SCLW/CMOS_Synthesizer/assets/exports/10-prng-cd4094-cd4070.pdf

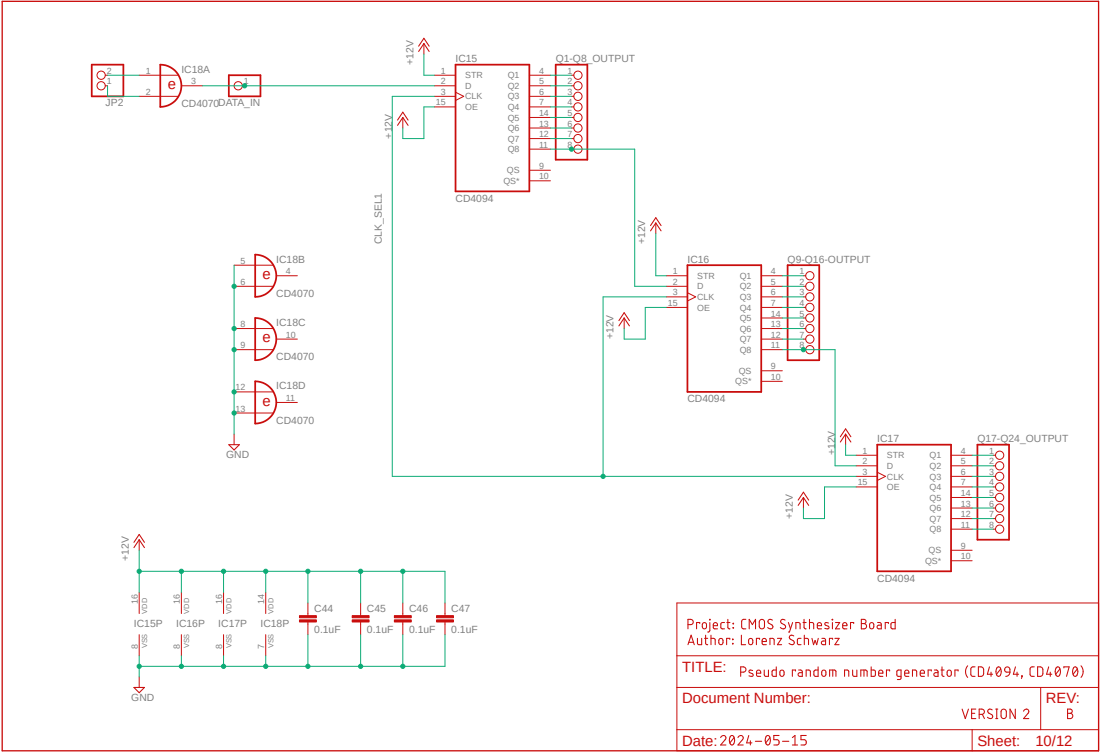
[picture p25: page 1]
