SCLW/CMOS_Synthesizer/assets/exports/11-mixing-section-lm358.pdf

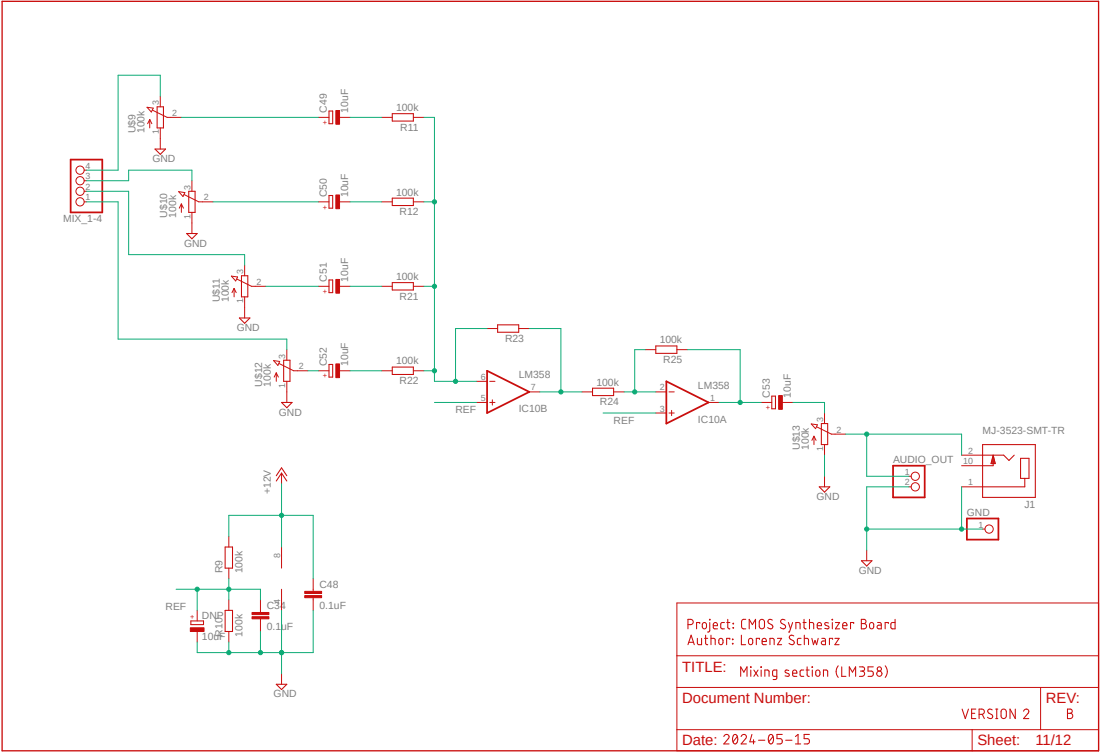
[picture p26: page 1]
