SCLW/CMOS_Synthesizer/assets/exports/12-rotary-switches.pdf

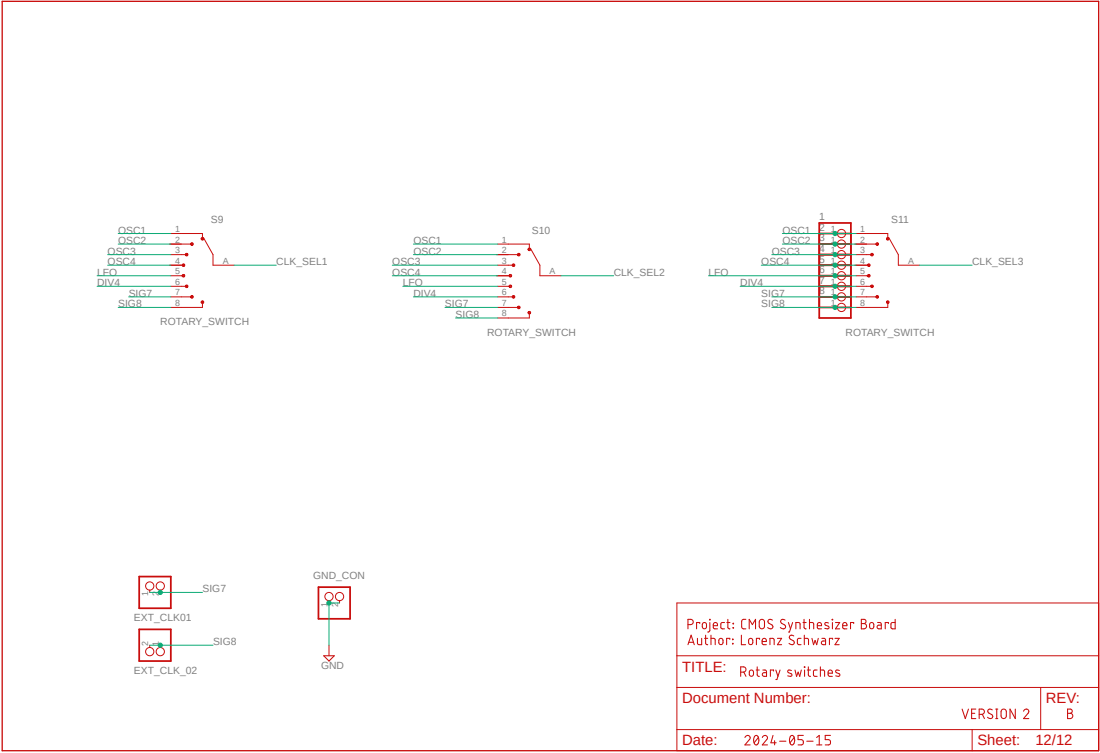
[picture p27: page 1]

Document Number: | REV:
