SCLW/CMOS_Synthesizer/assets/exports/deadlock-prevention-circuit-cd4068-cd4070-cd4077.pdf

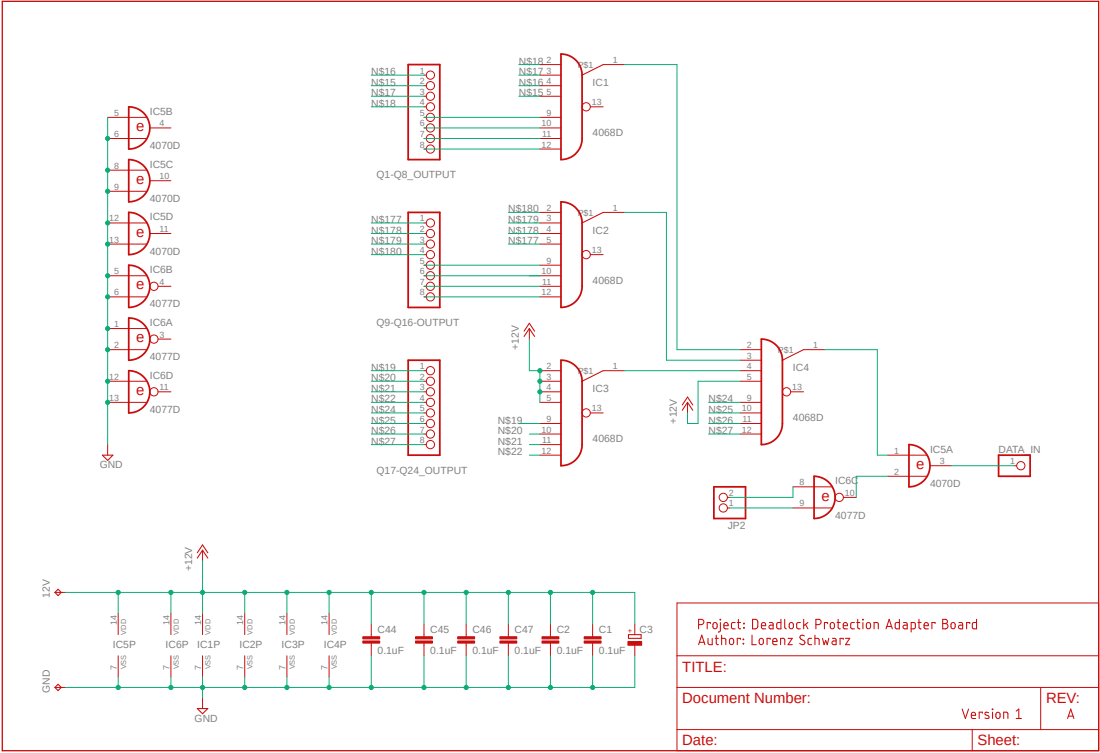
[picture p28: page 1]
