SCLW/CMOS_Synthesizer/assets/exports/dimensions.pdf

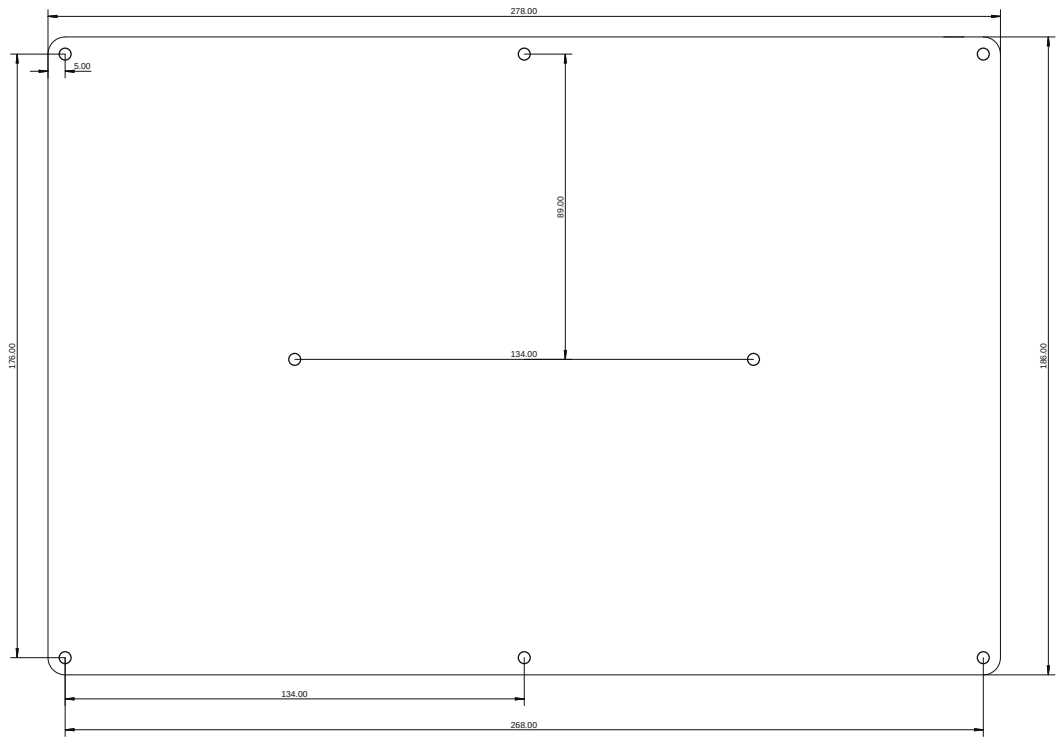
[picture p29: page 1]
