SCLW/CMOS_Synthesizer/assets/exports/main-board-traces.pdf

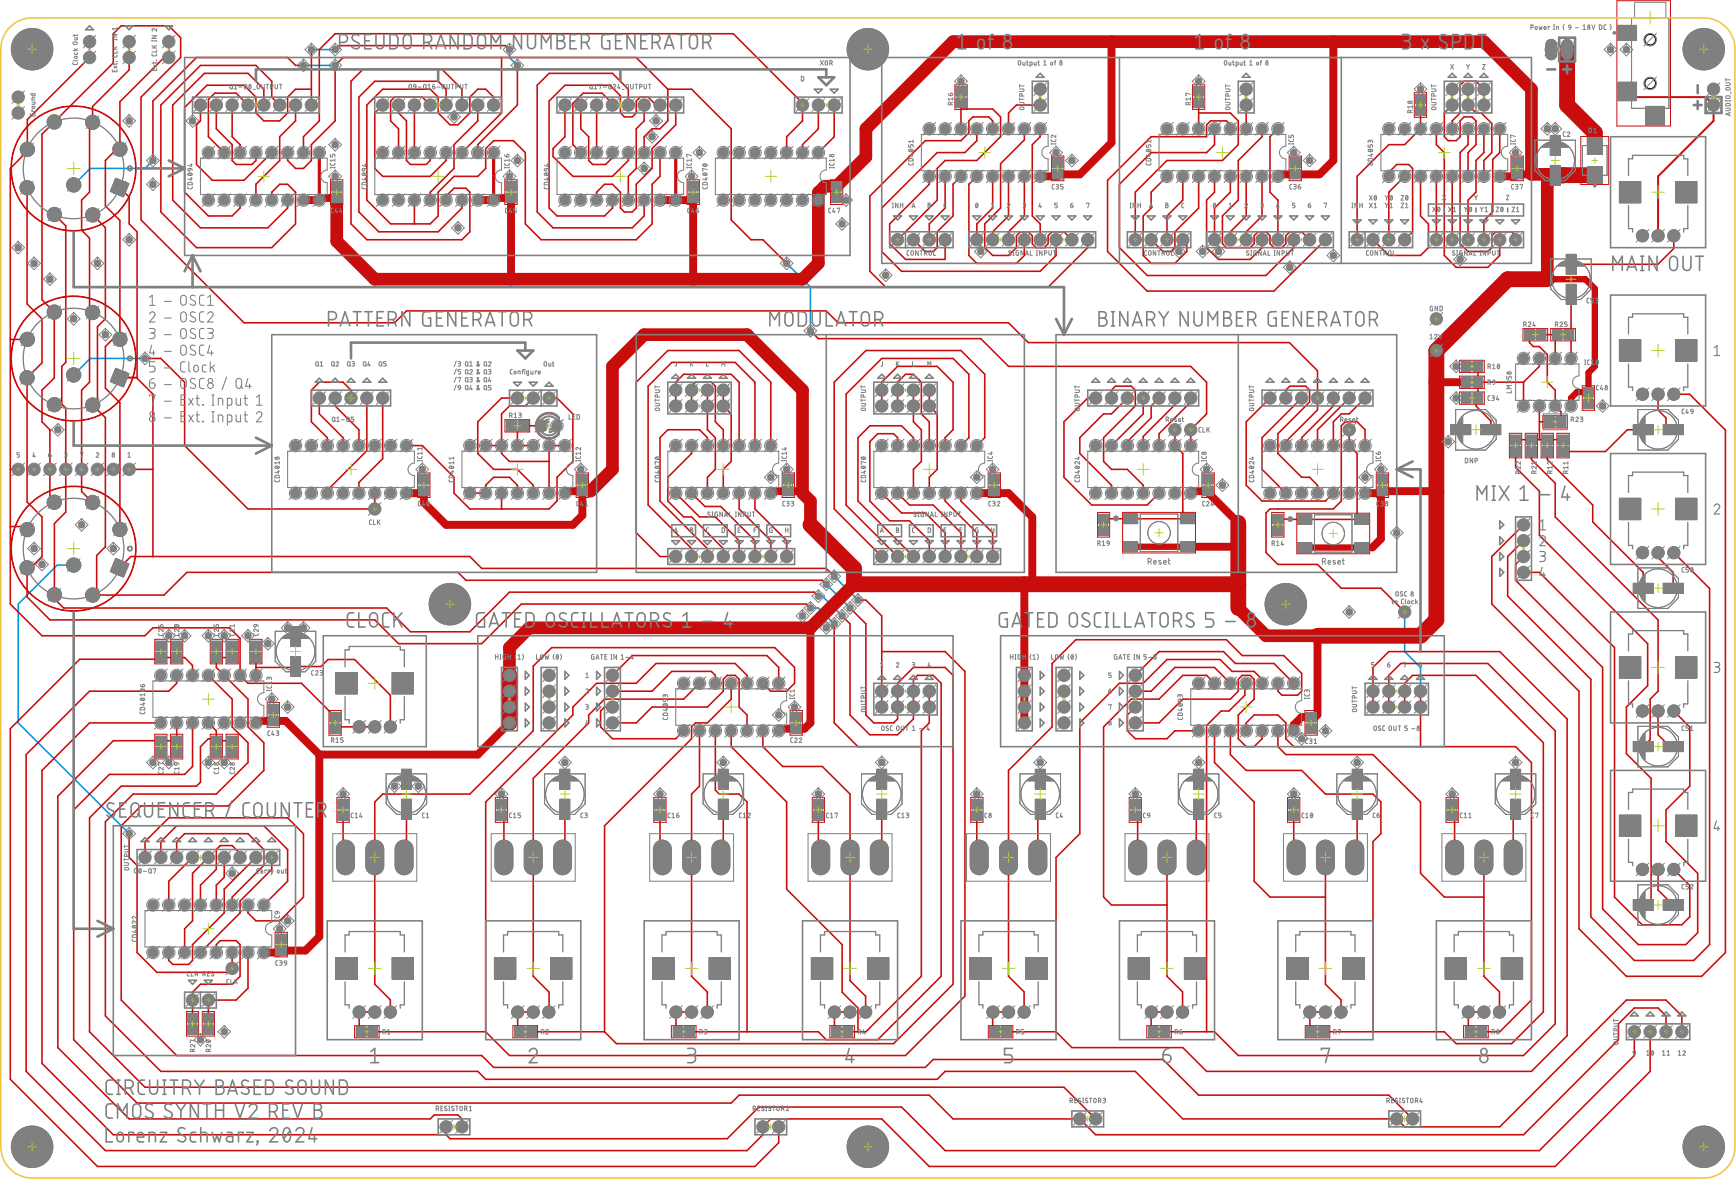
[picture p30: page 1]
